Nbrooks639/Voron-V2.5515/V2.5515 Sensorless cfg/Rapid Burner Rapido, Beacon/RapidoHF_Mount.stl

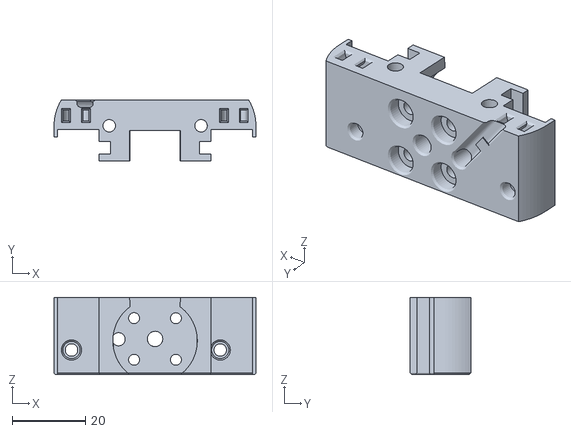
[picture p28: CAD file, 2023-07-29]
V2.5515 Sensorless cfg/Rapid Burner Rapido, Beacon/RapidoHF_Mount.stl
55.0 x 16.5 x 21.0
