Nbrooks639/Voron-V2.5515/V2.5515 Sensorless cfg/Hartk Zjoint mod/z_joint_ge5c_y_endstop_x1.stl

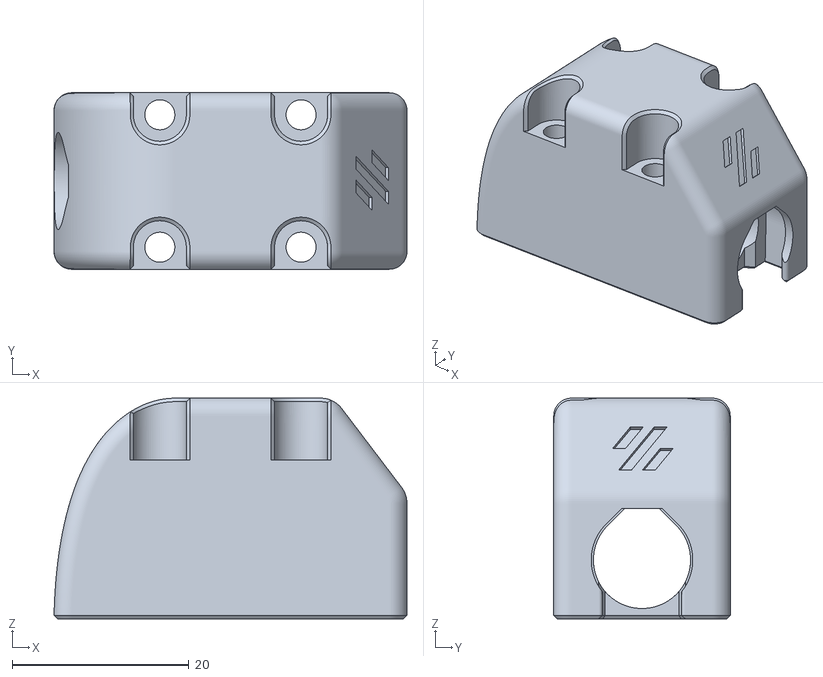
[picture p29: CAD file, 2023-09-22]
V2.5515 Sensorless cfg/Hartk Zjoint mod/z_joint_ge5c_y_endstop_x1.stl
40.0 x 20.0 x 25.0
