Nbrooks639/Voron-V2.5515/V2.5515 Sensorless cfg/Rapid Burner Rapido, Beacon/[c]_Diffuser.stl

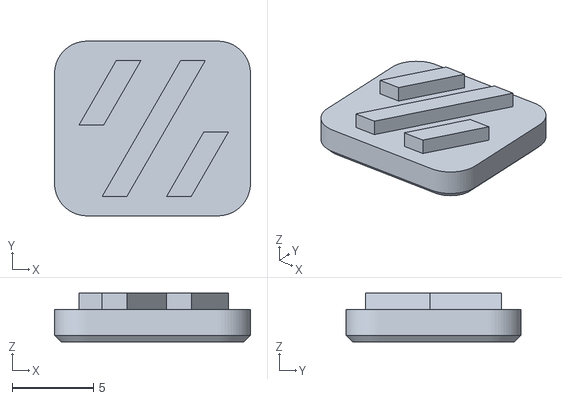
[picture p30: CAD file, 2023-07-29]
V2.5515 Sensorless cfg/Rapid Burner Rapido, Beacon/[c]_Diffuser.stl
12.1 x 10.7 x 3.00
