Nbrooks639/Voron-V2.5515/V2.5515 Sensorless cfg/Rapid Burner Rapido, Beacon/LGX_Lite_Mount.stl

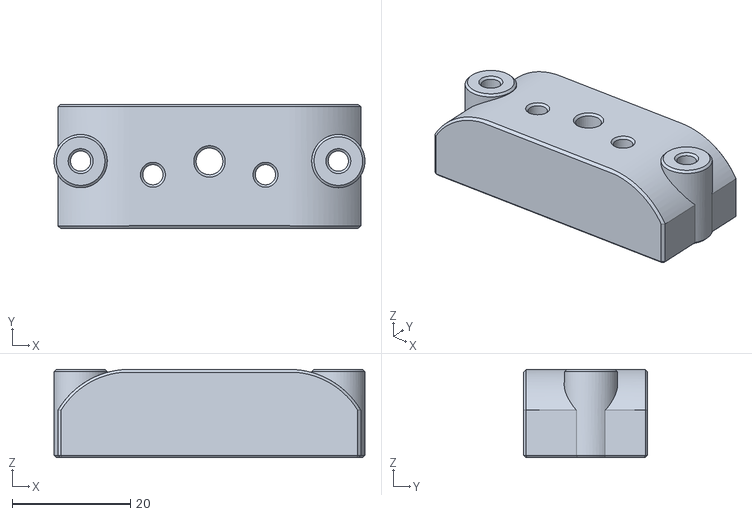
[picture p31: CAD file, 2023-07-29]
V2.5515 Sensorless cfg/Rapid Burner Rapido, Beacon/LGX_Lite_Mount.stl
52.5 x 21.0 x 14.9
