Nbrooks639/Voron-V2.5515/V2.5515 Sensorless cfg/Rapid Burner Rapido, Beacon/Probe_Bracket.stl

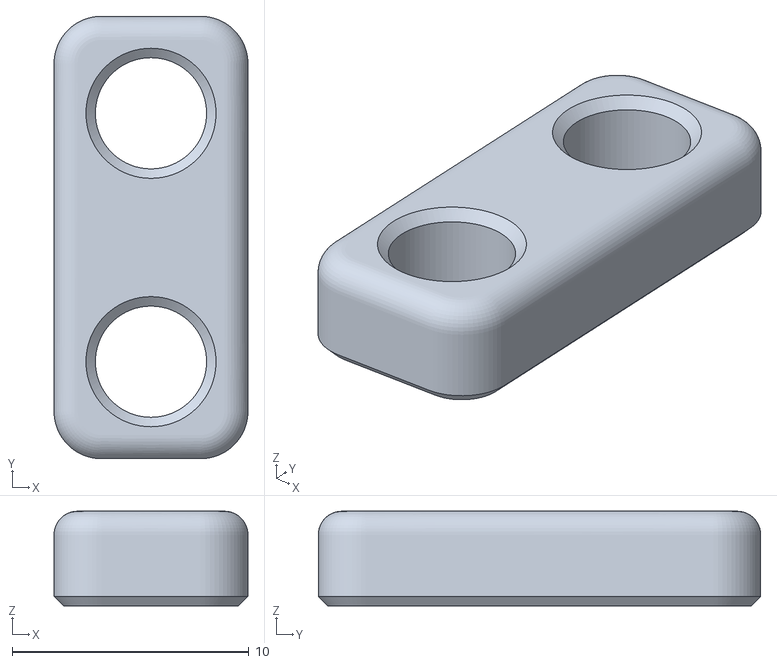
[picture p32: CAD file, 2023-07-29]
V2.5515 Sensorless cfg/Rapid Burner Rapido, Beacon/Probe_Bracket.stl
8.20 x 18.7 x 4.00
