Nbrooks639/Voron-V2.5515/V2.5515 Sensorless cfg/Rapid Burner Rapido, Beacon/Probe_Support.stl

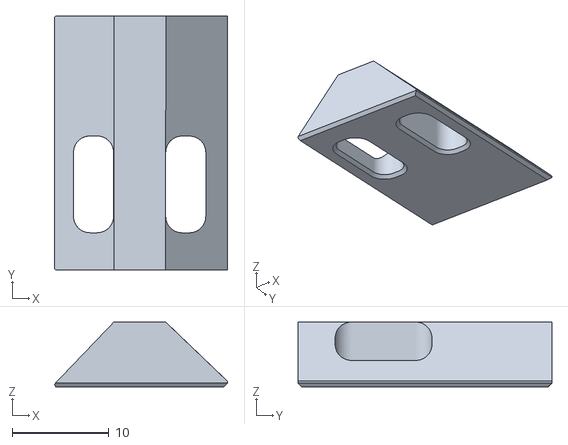
[picture p33: CAD file, 2023-07-29]
V2.5515 Sensorless cfg/Rapid Burner Rapido, Beacon/Probe_Support.stl
17.9 x 26.3 x 6.72
