Nbrooks639/Voron-V2.5515/V2.5515 Sensorless cfg/Rapid Burner Rapido, Beacon/Cowl_NoProbe.stl

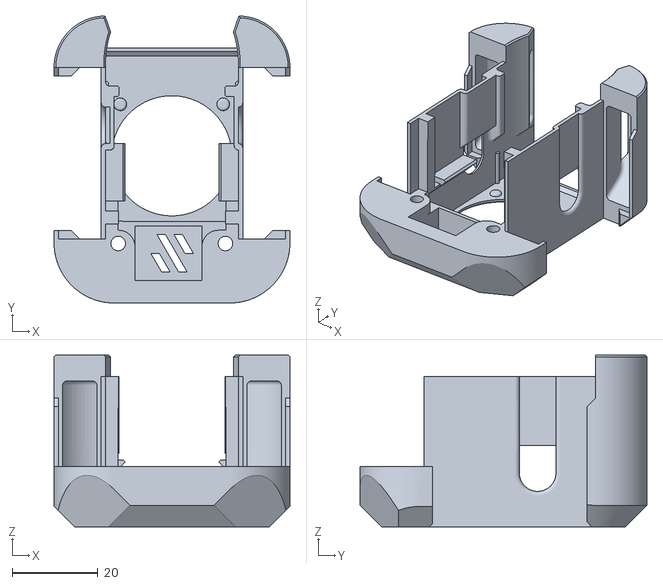
[picture p34: CAD file, 2023-07-29]
V2.5515 Sensorless cfg/Rapid Burner Rapido, Beacon/Cowl_NoProbe.stl
55.0 x 66.9 x 40.0
