Nbrooks639/Voron-V2.5515/V2.5515 Sensorless cfg/Rapid Burner Rapido, Beacon/HE_Fan Mount_Neopixel.stl

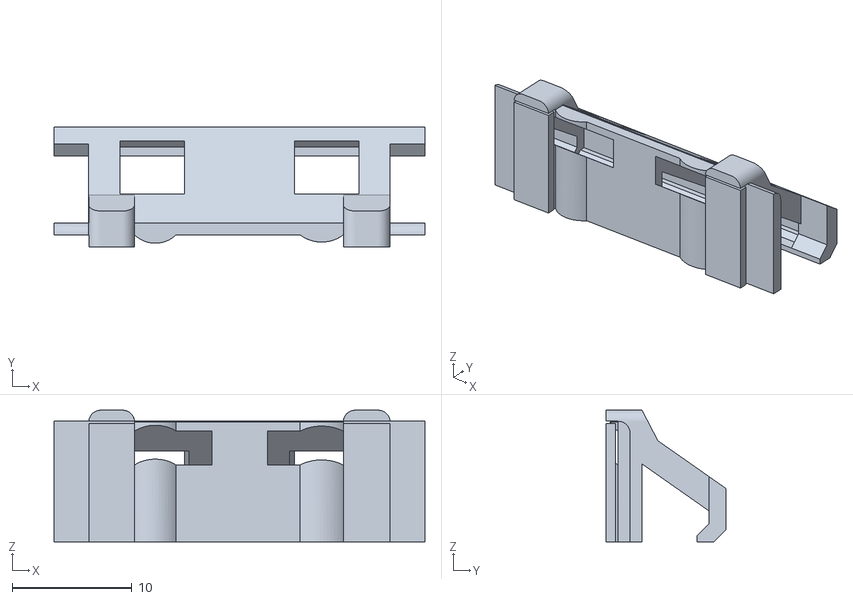
[picture p35: CAD file, 2023-07-29]
V2.5515 Sensorless cfg/Rapid Burner Rapido, Beacon/HE_Fan Mount_Neopixel.stl
31.0 x 10.0 x 11.0
