Nbrooks639/Voron-V2.5515/V2.5515 Sensorless cfg/macros.cfg

   
#####################################################################
#   print_start macro
#####################################################################

## *** THINGS TO UNCOMMENT: ***
## Bed mesh (2 lines at 2 locations)
## Z_TILT_ADJUST if your printer is a Trident
## Quad gantry level if your printer is a V2
## Nevermore - if you have one

[gcode_macro PRINT_START]
gcode:
  # This part fetches data from your slicer. Such as bed temp, extruder temp, chamber temp and size of your printer.
  {% set target_bed = params.BED|int %}
  {% set target_extruder = params.EXTRUDER|int %}
  #{% set target_chamber = params.CHAMBER|default("40")|int %}
  {% set x_wait = printer.toolhead.axis_maximum.x|float / 2 %}
  {% set y_wait = printer.toolhead.axis_maximum.y|float / 2 %}

  # Homes the printer, sets absolute positioning and updates the Stealthburner leds.
  STATUS_HOMING         # Sets SB-leds to homing-mode
  CLEAN_NOZZLE
  G28                   # Full home (XYZ)
  G90                   # Absolut position

  ##  Uncomment for bed mesh (1 of 2)
  BED_MESH_CLEAR       # Clears old saved bed mesh (if any)

  # Checks if the bed temp is higher than 90c - if so then trigger a heatsoak.
  {% if params.BED|int > 90 %}
    SET_DISPLAY_TEXT MSG="Bed: {target_bed}c"           # Displays info
    STATUS_HEATING                                      # Sets SB-leds to heating-mode
    M106 S200                                           # Turns on the PT-fan

    ##  Uncomment if you have a Nevermore.
    #SET_PIN PIN=nevermore VALUE=1                      # Turns on the nevermore

    G1 X{x_wait} Y{y_wait} Z15 F9000                    # Goes to center of the bed
    M190 S{target_bed}                                  # Sets the target temp for the bed
    

  # If the bed temp is not over 90c, then it skips the heatsoak and just heats up to set temp with a 5min soak
  {% else %}
    SET_DISPLAY_TEXT MSG="Bed: {target_bed}c"           # Displays info
    STATUS_HEATING                                      # Sets SB-leds to heating-mode
    #G1 X{x_wait} Y{y_wait} Z15 F9000                    # Goes to center of the bed
    M190 S{target_bed}                                  # Sets the target temp for the bed 
  {% endif %}

  # Heating nozzle to 150 degrees. This helps with getting a correct Z-home
  SET_DISPLAY_TEXT MSG="Hotend: 150c"          # Displays info
  M109 S150                                    # Heats the nozzle to 150c

  #  Uncomment for V2 (Quad gantry level AKA QGL)
  SET_DISPLAY_TEXT MSG="QGL"      # Displays info
  STATUS_LEVELING                 # Sets SB-leds to leveling-mode
  quad_gantry_level               # Levels the buildplate via QGL
  G28 Z                           # Homes Z again after QGL

  #  Uncomment for bed mesh (2 of 2)
  SET_DISPLAY_TEXT MSG="Bed mesh"    # Displays info
  STATUS_MESHING                     # Sets SB-leds to bed mesh-mode
  bed_mesh_calibrate                 # Starts bed mesh

  # Heats up the nozzle up to target via data from slicer
  SET_DISPLAY_TEXT MSG="Hotend: {target_extruder}c"             # Displays info
  STATUS_HEATING                                                # Sets SB-leds to heating-mode
  G1 X{x_wait} Y{y_wait} Z10 F9000                              # Goes to center of the bed
  M107                                                          # Turns off partcooling fan
  M109 S{target_extruder}                                       # Heats the nozzle to printing temp

  # Gets ready to print by doing a purge line and updating the SB-leds
  SET_DISPLAY_TEXT MSG="Printer goes brr"          # Displays info
  STATUS_PRINTING                                  # Sets SB-leds to printing-mode
  CLEAN_NOZZLE
  G0 X{x_wait - 50} Y4 F10000                      # Moves to starting point
  G0 Z0.4                                          # Raises Z to 0.4
  G91                                              # Incremental positioning 
  #VORON_PURGE
  G1 X80 E30 F1000                                # Purge line
  G90                                              # Absolut position
#####################################################################################################################################

#   Use PRINT_END for the slicer ending script - please customise for your slicer of choice
[gcode_macro PRINT_END]
gcode:
    {% set th = printer.toolhead %}
    {% set x_safe = th.position.x + 20 * (1 if th.axis_maximum.x - th.position.x > 20 else -1) %}
    {% set y_safe = th.position.y + 20 * (1 if th.axis_maximum.y - th.position.y > 20 else -1) %}
    {% set z_safe = [th.position.z + 2, th.axis_maximum.z]|min %}
    
    SAVE_GCODE_STATE NAME=STATE_PRINT_END
    
    M400                           ; wait for buffer to clear
    G92 E0                         ; zero the extruder
    G1 E-12.0 F1800                 ; retract filament
    
    TURN_OFF_HEATERS
    
    G90                                      ; absolute positioning
    G0 X{x_safe} Y{y_safe} Z{z_safe} F30000  ; move nozzle to remove stringing
    G0 X{th.axis_maximum.x//2} Y{th.axis_maximum.y - 2} F3600  ; park nozzle at rear
    M107                                     ; turn off fan

    RESTORE_GCODE_STATE NAME=STATE_PRINT_END
    G4 S3                          ; wait 3 seconds
    M18                            ; disable motors

###############################################################################################


[gcode_macro QUAD_GANTRY_LEVEL]
rename_existing: QUAD_GANTRY_LEVEL_BASE
gcode:
    QUAD_GANTRY_LEVEL_BASE horizontal_move_z=10 retry_tolerance=1.000
    QUAD_GANTRY_LEVEL_BASE horizontal_move_z=2

#########################################################################

[gcode_macro M109]
rename_existing: M99109
gcode:
    #Parameters
    {% set s = params.S|float %}
    
    M104 {% for p in params %}{'%s%s' % (p, params[p])}{% endfor %}  ; Set hotend temp
    {% if s != 0 %}
      TEMPERATURE_WAIT SENSOR=extruder MINIMUM={s} MAXIMUM={s+1}   ; Wait for hotend temp (within 1 degree)
    {% endif %}

###############################################################################

[gcode_macro CLEAN_NOZZLE]
## voron 2.4 300 ###
variable_start_x: 236.50
variable_start_y: 296.00
variable_start_z: 3.50
variable_wipe_dist: 40
variable_wipe_qty: 4
variable_wipe_spd: 150
variable_raise_distance: 10

gcode:
 {% if "xyz" not in printer.toolhead.homed_axes %}
   G28
 {% endif %}
 
 G90                                            ; absolute positioning
 ## Move nozzle to start position
 G1 X{start_x} Y{start_y} F6000
 G1 Z{start_z} F1500

 ## Wipe nozzle
 {% for wipes in range(1, (wipe_qty + 1)) %}
   G1 X{start_x + wipe_dist} F{wipe_spd * 60}
   G1 X{start_x} F{wipe_spd * 60}
 {% endfor %}

 ## Raise nozzle
 G1 Z{raise_distance}

################################################################################

[gcode_macro UNLOAD_FILAMENT]
gcode:
   
   M83                            ; set extruder to relative
   G1 E8 F300                     ; extrude a little to soften tip
   G1 E-45 F1800                  ; retract some, but not too much or it will jam
   M82                            ; set extruder to absolute
   #M104 S0                        ; turn off hot end

#################################################################################

[gcode_macro M600]
description: Filament change
gcode: PAUSE X=10 Y=10 Z_MIN=50

###############################################################################

[gcode_macro GET_PROBE_LIMITS]
description: Calculates the probe min/max/current coordinates
gcode: 
    {% set config = printer.configfile.settings %}
    # Find probe config in configfile
    {% if config["bltouch"] %}
        # bltouch section found
        {% set probe = config["bltouch"] %}
        {% set has_probe = True %}
    {% elif config["probe"] %}
        # probe section found
        {% set probe = config["probe"] %}
        {% set has_probe = True %}
    {% elif config["beacon"] %}
        # probe section found
        {% set probe = config["beacon"] %}
        {% set has_probe = True %}
    {% else %}
        # No probe or bltouch sections found
        RESPOND MSG="Failed to detect probe in configfile"
    {% endif %}
    {% if has_probe %}
        {% set stepperx = config["stepper_x"] %}
        {% set steppery = config["stepper_y"] %}
        {% set xprobemin = stepperx["position_min"]|float + probe["x_offset"]|float %} 
        {% set xprobemax = stepperx["position_max"]|float + probe["x_offset"]|float %} 
        {% set yprobemin = steppery["position_min"]|float + probe["y_offset"]|float %} 
        {% set yprobemax = steppery["position_max"]|float + probe["y_offset"]|float %}
        RESPOND MSG="Configured Probe X-Offset {probe.x_offset}"
        RESPOND MSG="Configured Probe Y-Offset {probe.y_offset}"
        {% if probe.z_offset is defined %}
            RESPOND MSG="Configured Probe Z-Offset {probe.z_offset}"
        {% elif probe.trigger_distance is defined %}
            RESPOND MSG="Configured Probe Trigger Distance {probe.trigger_distance}"
        {% endif %}
        RESPOND MSG="Minimum PROBE position X={xprobemin} Y={yprobemin}" 
        RESPOND MSG="Maximum PROBE position X={xprobemax} Y={yprobemax}"
        # check if printer homed
        {% if "xyz" in printer.toolhead.homed_axes %} 
            {% set curprobex = printer.toolhead.position.x|float + probe["x_offset"]|float %} 
            {% set curprobey = printer.toolhead.position.y|float + probe["y_offset"]|float %} 
            RESPOND MSG="Current PROBE position X={curprobex} Y={curprobey}"
        {% endif %}
    {% endif %}
################################################################################################

[gcode_macro LOAD_FILAMENT]
gcode:
    {% set speed = params.SPEED|default(300) %}
    {% set max_velocity = printer.configfile.settings['extruder'].max_extrude_only_velocity %}
    SAVE_GCODE_STATE NAME=load_state
    M300 # beep
    G91
    G92 E0
    G1 E12 F{max_velocity} # fast-load
    G1 E10 F{speed} # purge
    M300
    M300
    RESTORE_GCODE_STATE NAME=load_state


##################################################################################################################
#########################################%%%$$$$$$$$$$$$$$$#########################################################
## BTT KnOmI  ###

[gcode_macro BED_MESH_CALIBRATE]
rename_existing: BED_MESH_CALIBRATE_BASE
variable_probing:False
gcode:
    SET_GCODE_VARIABLE MACRO=BED_MESH_CALIBRATE VARIABLE=probing VALUE=True
    BED_MESH_CALIBRATE_BASE
    SET_GCODE_VARIABLE MACRO=BED_MESH_CALIBRATE VARIABLE=probing VALUE=False

# # ## KNOMI QGL (replace your existing gcode_macro for QUAD_GANTRY_LEVEL)

[gcode_macro QUAD_GANTRY_LEVEL]
rename_existing: QGL_BASE
gcode:
    SET_GCODE_VARIABLE MACRO=BED_MESH_CALIBRATE VARIABLE=probing VALUE=True
    STATUS_LEVELING
    QGL_BASE {rawparams}
    STATUS_READY
    SET_GCODE_VARIABLE MACRO=BED_MESH_CALIBRATE VARIABLE=probing VALUE=False
	
############################################################################################

[gcode_macro SET_ACTIVE_SPOOL]
gcode:
  {% if params.ID %}
    {% set id = params.ID|int %}
    {action_call_remote_method(
       "spoolman_set_active_spool",
       spool_id=id
    )}
  {% else %}
    {action_respond_info("Parameter 'ID' is required")}
  {% endif %}

#################################################################

[gcode_macro CLEAR_ACTIVE_SPOOL]
gcode:
  {action_call_remote_method(
    "spoolman_set_active_spool",
    spool_id=None
  )}

################################################################

# [filament_switch_sensor switch_sensor]
# switch_pin: ^PC15
# pause_on_runout: True
# runout_gcode:
#   PAUSE # [pause_resume] is required in printer.cfg
#   M117 Filament switch runout
# insert_gcode:
#   M117 Filament switch inserted

# ################################################################################

# [filament_motion_sensor encoder_sensor]
# switch_pin: ^PF1
# detection_length: 2.88
# extruder: extruder
# pause_on_runout: True
# runout_gcode:
#   PAUSE # [pause_resume] is required in printer.cfg
#   M117 Filament encoder runout
# insert_gcode:
#   M117 Filament encoder inserted

########################################################################


  
